qteck/Altium-Projects/Optical_receiver_design/LTSPICE/LPF.asc

C2: cap
R1: res
V1: voltage; SINE(0 1 1e6); AC 1
Named nets: 0, Vin
