qteck/Altium-Projects/Optical_receiver_design/LTSPICE/stage-1-PowerProtection.asc

C1: cap; 0.33µ
C2: cap; 0.1µ
C3: cap; 0.33µ
C4: cap; 0.1µ
D1: diode
D2: diode
D3: diode
D4: diode
D5: diode
D6: diode
D9: diode
D10: diode
R1: res; 2.2k
R2: res; 2.2K
R3: res; 33K
R4: res; 33K
R5: res; 2.2K
R6: res; 2.2K
R7: res; 1k
R8: res; 1k
U1: opamp
U2: opamp
V1: voltage; 15V
V2: voltage; 24
Named nets: 0
.dc V1 8V 15V 0.5
.lib opamp.sub
