qteck/Altium-Projects/Optical_receiver_design/LTSPICE/stage-2-LM6171A-inverting-op-amp.asc

C1: cap; 8p
C2: cap; 0.1n
C3: cap; 0.1n
C4: cap; 2.2µ
C5: cap; 2.2µ
C6: cap; 22n
I1: current; SINE(0 1u 1e6 0); AC 1u
R1: res; 4.7k
R2: res; 3k3
U1: opamp2; LM318
V1: voltage; 12
V2: voltage; -12
Named nets: V+, 0, V-, Vin, Vout
.include components/LM318.txt
.ac dec 2 1 20e6
