qteck/Altium-Projects/Optical_receiver_design/LTSPICE/stage-3-HPF-DC-Blocker.asc

C1: cap; 22n
R1: res; 4k7
V1: voltage; SINE(0 1m 1e6); AC 1m
Named nets: 0, Vin
.ac dec 3m 1 10k
