qteck/Altium-Projects/Optical_receiver_design/LTSPICE/stage-4-LM318-sullen-key - only.asc

C1: cap; 56p
C2: cap; 56p
C3: cap; 100p
C4: cap; 100p
C6: cap; 68p
C7: cap; 1n
C9: cap; 2.2µ
C10: cap; 0.1n
C11: cap; 2.2µ
C12: cap; 0.1n
R1: res; 2.2k
R2: res; 1.7k
R3: res; 470
R4: res; 470
R5: res; 1.8k
R6: res; 1.4k
R7: res; 220
R8: res; 220
R10: res; 10k
R11: res; 330
R12: res; 1.5k
R13: res; 100k
U1: opamp2; LM6171A/NS
U2: opamp2; LM6171A/NS
U3: opamp2; LM6171A/NS
V1: voltage; 12
V2: voltage; -12
V3: voltage; SINE(0 125mv 1e6); AC 125mv
Named nets: 0, V+, V-, Vout, Vout2, InV
.include components/LM6171A.txt
.ac dec 3u 1 40e6
