qteck/Altium-Projects/Optical_receiver_design/LTSPICE/stage-4-LM318-sullen-key-linked.asc

C1: cap; 100p
C2: cap; 100p
C3: cap; 100p
C4: cap; 100p
C5: cap; 22n
C6: cap; 22p
C7: cap; 27p
C8: cap; 8p
C9: cap; 2.2µ
C10: cap; 0.1n
C11: cap; 2.2µ
C12: cap; 0.1n
I1: current; SINE(0 100u 1e6); AC 1e6
R1: res; 2k
R2: res; 1k
R3: res; 270
R4: res; 270
R5: res; 1k
R6: res; 2k
R7: res; 270
R8: res; 270
R9: res; 4k7
R10: res; 10k
R11: res; 1k2
R12: res; 1k
R13: res; 100k
R14: res; 3k3
U1: opamp2; LM6171A/NS
U2: opamp2; LM6171A/NS
U3: opamp2; LM6171A/NS
U4: opamp2; LM318
V1: voltage; 12
V2: voltage; -12
Named nets: 0, Iin, V+, V-, Vout
.include components/LM6171A.txt
.include components/LM318.txt
.ac dec 10 1 10e6
