qteck/Altium-Projects/Optical_receiver_design/LTSPICE/stage-5-LM6171A-post-inverting-op-amp.asc

C1: cap; 26.5p
C2: cap; 1.59n
R1: res; 10k
R2: res; 100k
R3: res; 1k
R4: res; 1k
U1: opamp2; LM6171A/NS
V1: voltage; 12
V2: voltage; -12
V3: voltage; SINE(0 10m 1e6); AC 10m
Named nets: V+, 0, V-, Vin, Vout
.include components/LM6171A.txt
.ac dec 10 1 10e6
